rockyroadshub/ACFC/Essentials/Features/ACFC Device.gif

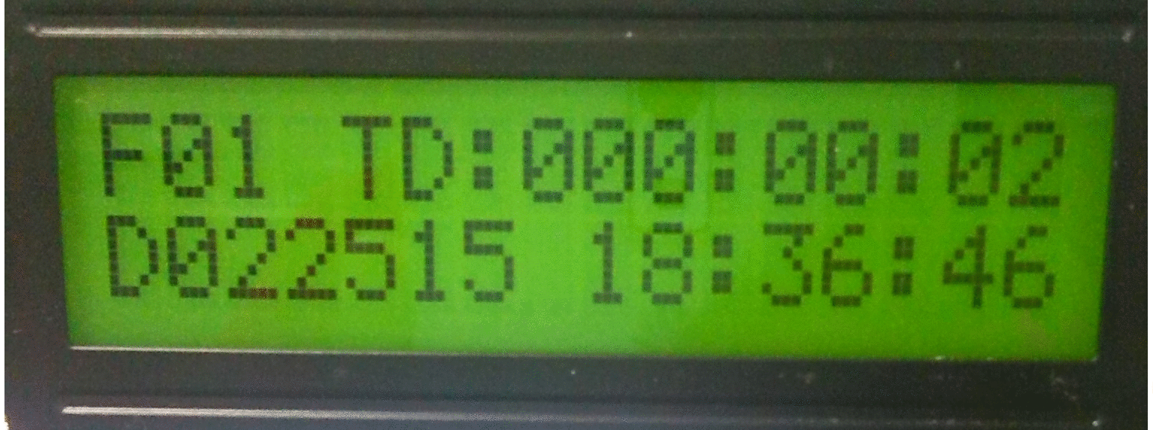
Essentials/Features/ACFC Device.gif
