rockyroadshub/ACFC/Essentials/Features/Device Lock.jpg

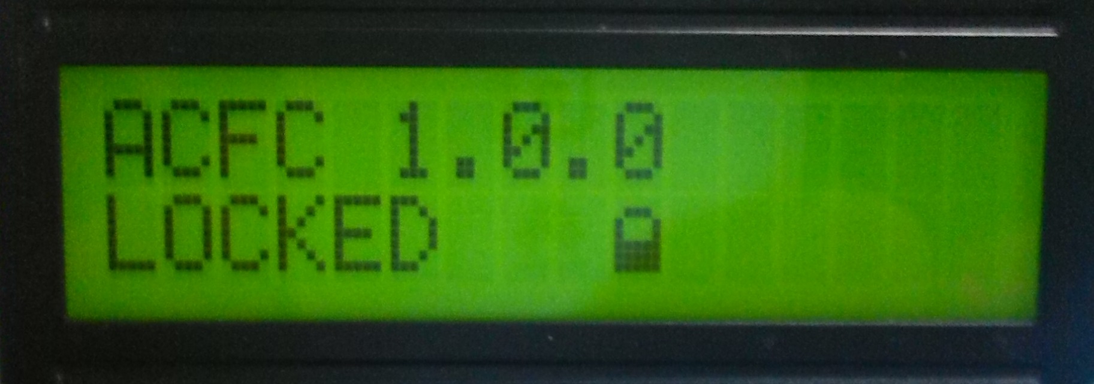
Essentials/Features/Device Lock.jpg
