rockyroadshub/ACFC/Essentials/Features/Device Unlock.jpg

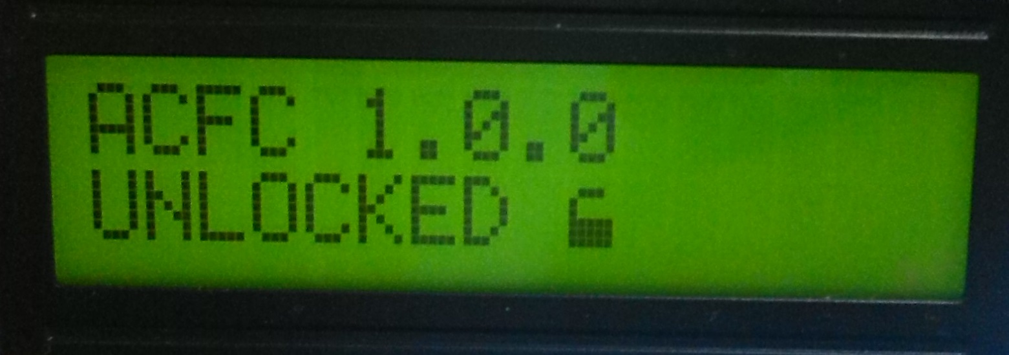
Essentials/Features/Device Unlock.jpg
