rockyroadshub/ACFC/Essentials/Features/Fluctuation Timer and Counter 1.jpg

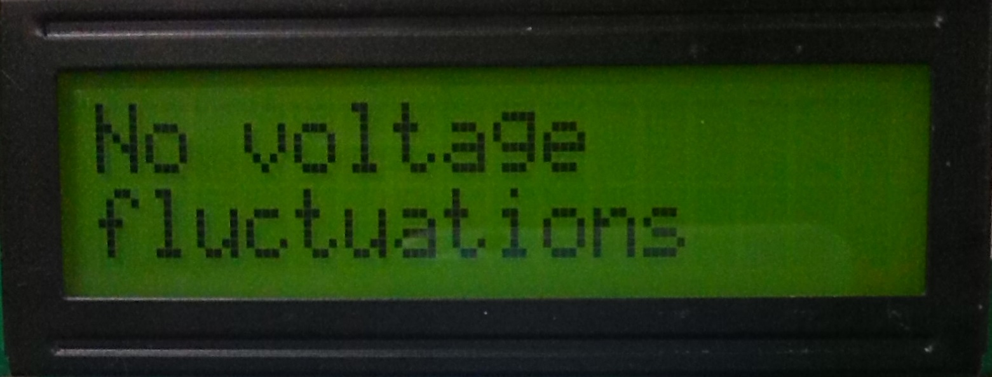
Essentials/Features/Fluctuation Timer and Counter 1.jpg
