rockyroadshub/ACFC/Essentials/Features/Fluctuation Timer and Counter 2.jpg

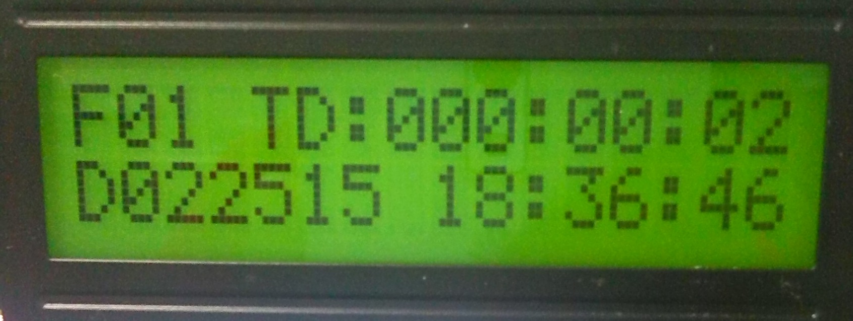
Essentials/Features/Fluctuation Timer and Counter 2.jpg
