rockyroadshub/ACFC/Essentials/Features/System Time and Date.jpg

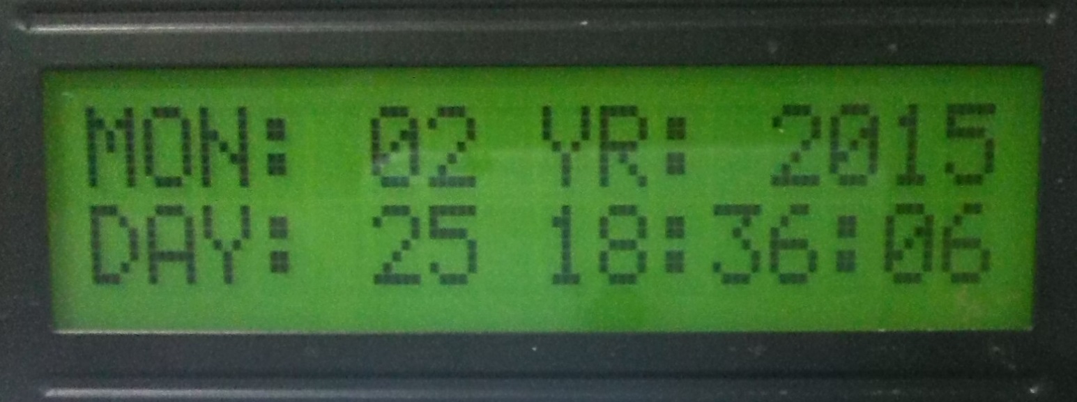
Essentials/Features/System Time and Date.jpg
