rockyroadshub/ACFC/Essentials/Model/ACFC.png

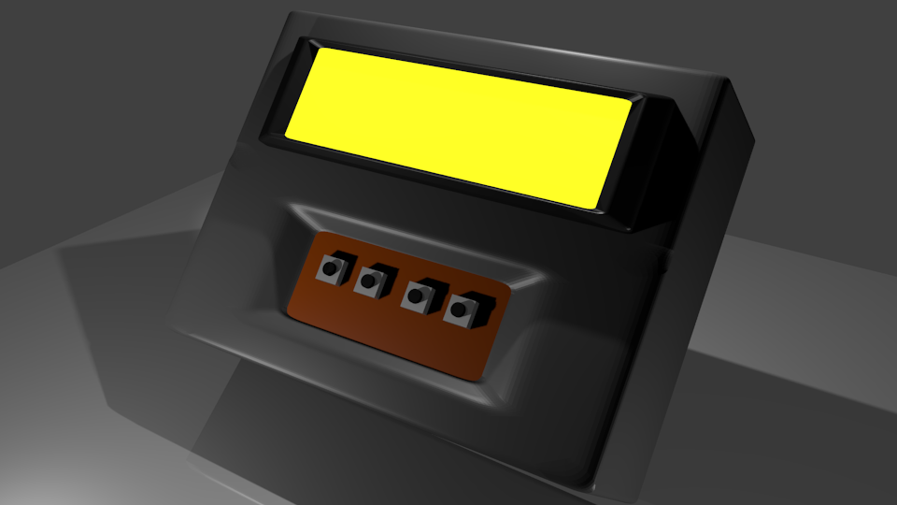
Essentials/Model/ACFC.png
