rockyroadshub/ACFC/Essentials/Others/Buttons.jpg

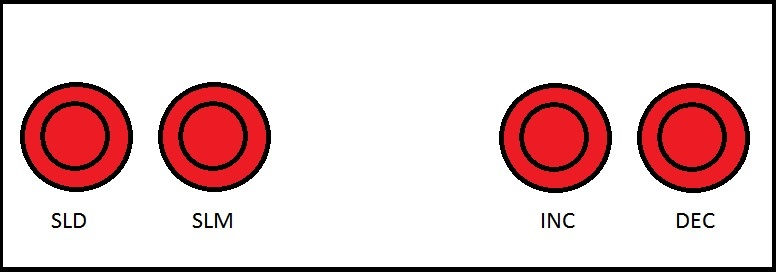
Essentials/Others/Buttons.jpg
