rockyroadshub/ACFC/Manuals/Gizduino Installation Guide.pdf

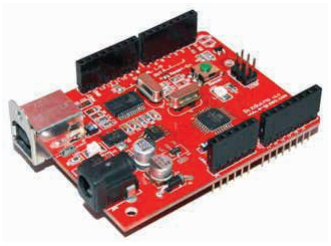
[picture p33: figure]
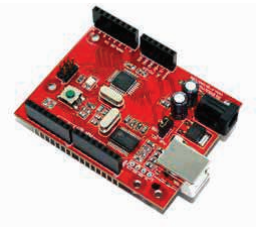
[picture p34: figure]

Page 1 of 4 Pages | gizDuino Installation Guide

# gizDuino

# Installation Guide

For gizDuino 168/328 Ver 3.0

gizDuino platform is based on open source Arduino platform designed by Massimo Banzi, et al. It is not an exact copy though, but the user will not notice any difference during normal use. Once the driver is successfully installed, the gizDuino will function exactly like an Arduino. The important thing is, the right driver must be installed in the right manner. Failure to do this simple procedure would almost certainly results in problems.

USB Interface

The Arduino uses an FT-232 chip as its USB bridge. In contrast, the gizDuino uses the PL-2303 chip. PL-2303 was picked over the FT-232 since they are easier to source, at least from our region. This difference will be visible to the user only during device driver installation.

!"#$%&'()'*+(&",,(#%-".*(-/0-(-/*(1+'-(-"2*(-/*(3"4-Duino is plugged in a PC, the Windows OS will automatically make an attempt to install its own driver. And will usually complete the procedure without 5033"#3(0#(*++%+6(7/*(8+%9,*2("':(3"4;)"#%(&",,(#%-( work with the Windows built-in driver. You must install the latest the driver provided with the gizDuino.

Figure 1. gizDuino 168/328 Ver. 3.0 now features automatic power source selection and an optiboot bootloader.

Figure 2. Previous versions of the gizDuino require the user to manually change jumper settings to switch to a different power source.

Copyright 2012 by e-Gizmo Mechatronix Central.

Arduino is an open source platform developed by the Arduino Team (Dave Mellis, Tom Igoe, Gianluca Martino, David Cuartielles, and Massimo Banzi) . www.arduino.cc

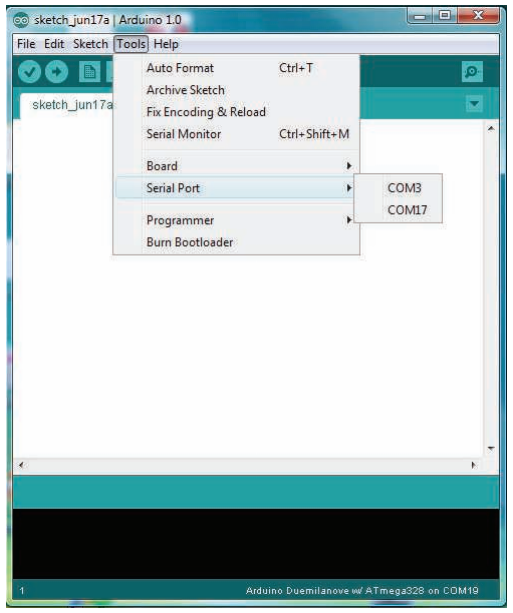
[picture p35: figure]
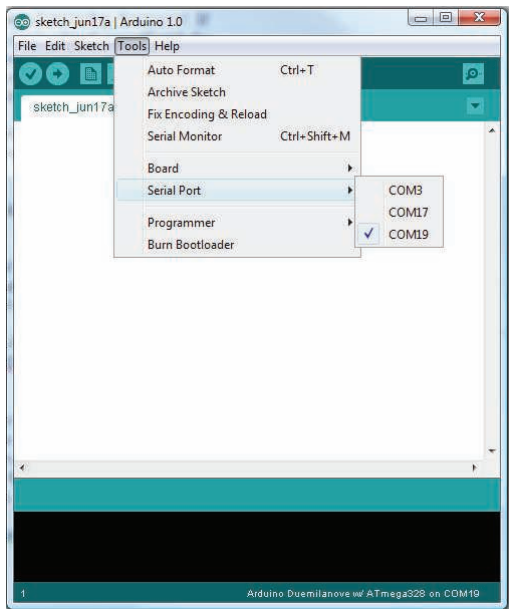
[picture p36: figure]

gizDuino Installation Guide | Page 2 of 4 Pages

Driver Installation

Driver installation must be done before connecting the gizDuino with your PC. But then,we have this "++*'"'-"9,*()+3*(%<(8,)33"#3(-/"#3'(1+'-(9*<%+*(+*0$-ing the manual. You already plugged your gizDuino, didn’t you? Not to worry, it is nothing to be embarrassed about. No permanent harm done either, it is just you burdened yourself with the extra work needed to undo your mistake – you have to uninstall the wrong driver. It is easy, just uninstall the PL-2303 com port appearing in your system device driver list. If you have no idea how to do this, have someone to do it for you.

7%("#'-0,,:(,%0$(-/*("#'-0,,0-"%#(=;(0#$(1#$(-/*(<%,$*+( with a PL2303 on its label, and run the setup.exe contained in it. Follow the setup instructions that 50'/*'(%#(>%)+('.+**#:(0#$(>%)(0+*($%#*6(

COM port Assignment

Don’t plug your gizDuino just yet, we have to determine what COM port it is assigned tyo:

1. Launch the Arduino IDE.

### 2. Click Tools>Serial Port and record the list of

available COM ports. (See Note 1)

### 3. Click anywhere within the Arduino IDE window

to close the drop menu.

### 4. Plug the gizDuino. Let the PC does its job of

recognizing the gizDuino. This may take a few seconds.

### 5. Click Tools>Serial Port once again and look

for a new COM port added to the list. This is the COM assignment of your gizDuino. Click to select if it is not marked with a check mark.

Figure 3. Available COM ports as displayed from my PC before the gizDuino is plugged in. See Note 1.

Figure 4. COM19 appears after plugging in my gizDuino. A different COM port may be assigned by your PC depending on its availability.

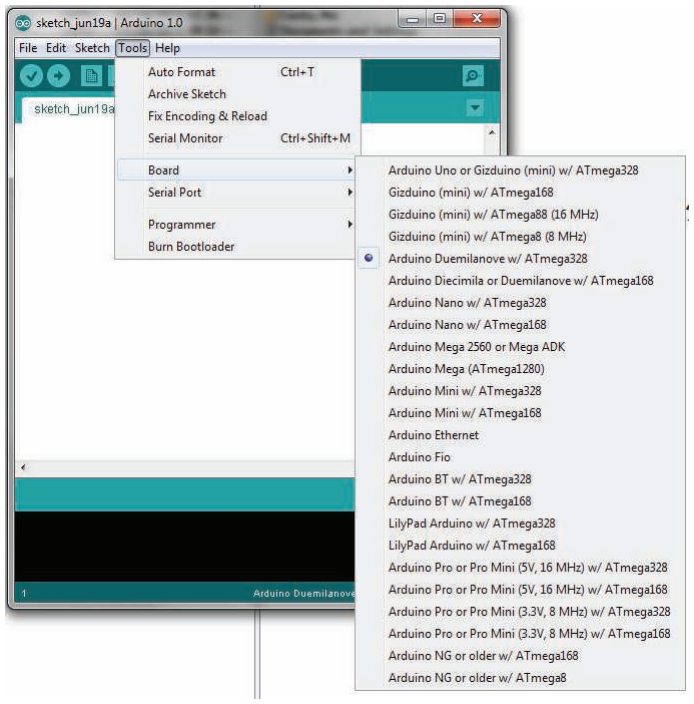
[picture p37: figure]

Page 3 of 4 Pages | gizDuino Installation Guide

Board Assigment

!*(0+*(0,2%'-(-/*+*6(7/*(1#0,('-*8(&",,(9*(-%(-*,,(-/*( Arduino IDE what Arduino hardware you are using. If you are using an Arduino IDE provided by e-Gizmo, just select the gizDuino model corresponding to your board. If you acquired it elsewhere, don’t look for gizDuino boards in the list, there is none. Select the equivalent as follows:

gizDuino 328 rev 3.0 -> Arduino Uno

If you are using and older version of gizDuino:

gizDuino 328
-> Arduino Duemilanove w/ ATmega328

gizDuino 168
-> Arduino Diecimila or Duemilanove w/ ATmega168

Your gizDuino is now ready to use! This procedure need to be done only once. Once the setup is correctly completed, your gizDuino will be remembered by the Arduino IDE for as long as you want it to be remembered.

Figure 5. Select the gizDuino model corresponding to your board. If the gizDuino boards do not appear in the list, select the Arduino equivalent as described in the text.

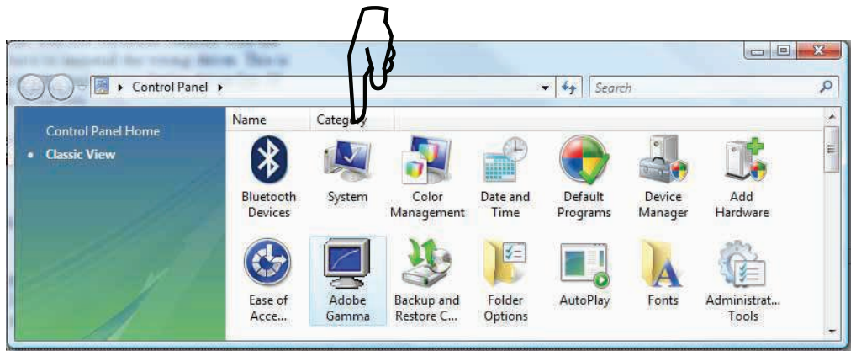
[picture p38: figure]
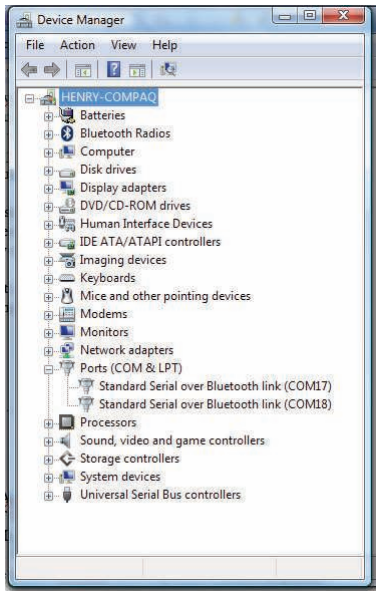
[picture p39: figure]

gizDuino Installation Guide | Page 4 of 4 Pages

Note 1:

The Arduino IDE can easily be distracted from too many unused COM port. If you use a lot of Bluetooth devices with your PC, chances are, your system is littered with too many COM port. This can slow down the port scanning of the Arduino IDE almost to a halt. You will notice this whenever you click Tools on the menu bar. It will take a long while before Arduino IDE responds with the drop menu.

To remedy this, uninstall all Bluetooth COM ports that are not in use.

Figure 6. If your Arduino IDE suddenly runs slow on click to the Tools menu, chances are your system is choked by too many COM ports assigned to unused Bluetooth devices. Check your system COM usage by clicking Control Panel>System>Device Drivers.

Figure 7. Click Ports to display COM ports usage. Remove all COM ports assigned to unused Bluetooth devices to speed up the Arduino.
