rockyroadshub/ACFC/Essentials/Others/Printer USB Connector.jpg

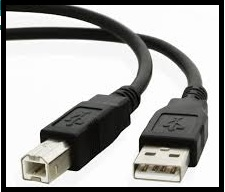
Essentials/Others/Printer USB Connector.jpg
