rockyroadshub/ACFC/Essentials/PCB/Button PCB/Etch/Button PCB_etch_silk_bottom.pdf

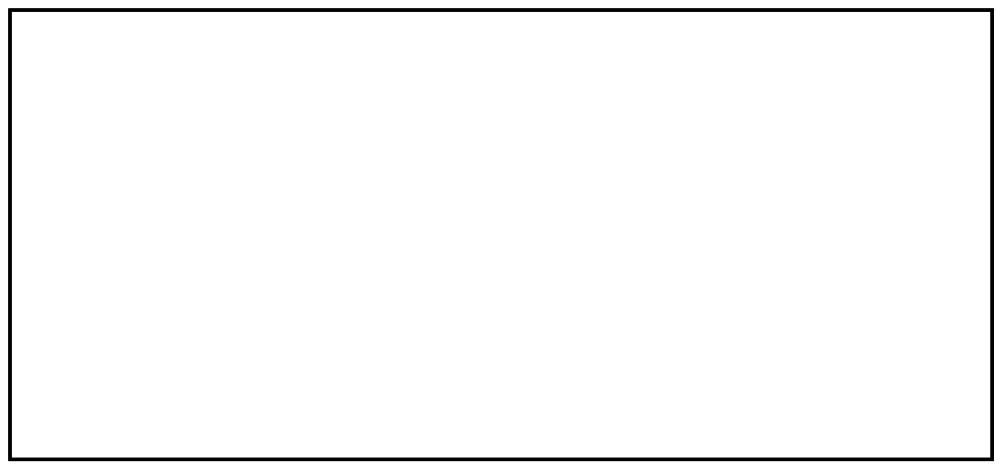
[picture p59: page 1]
