rockyroadshub/ACFC/Essentials/PCB/Button PCB/Etch/Button PCB_etch_silk_bottom_mirror.pdf

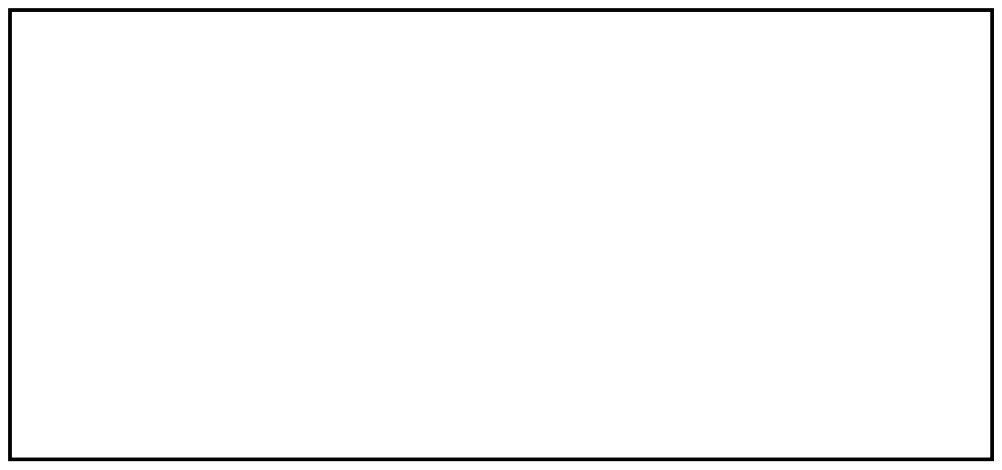
[picture p60: page 1]
