rockyroadshub/ACFC/Essentials/PCB/Button PCB/Etch/Button PCB_etch_silk_top.pdf

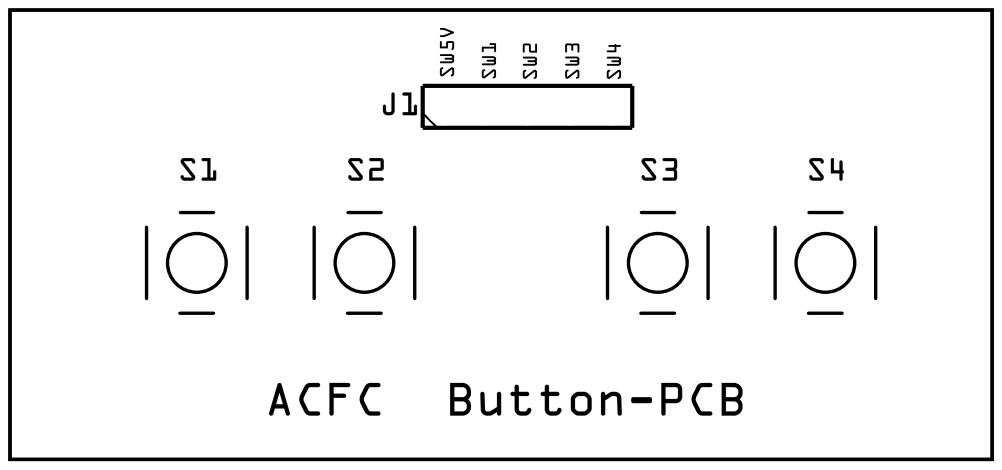
[picture p61: page 1]
