rockyroadshub/ACFC/Essentials/PCB/Button PCB/Etch/Button PCB_etch_silk_top_mirror.pdf

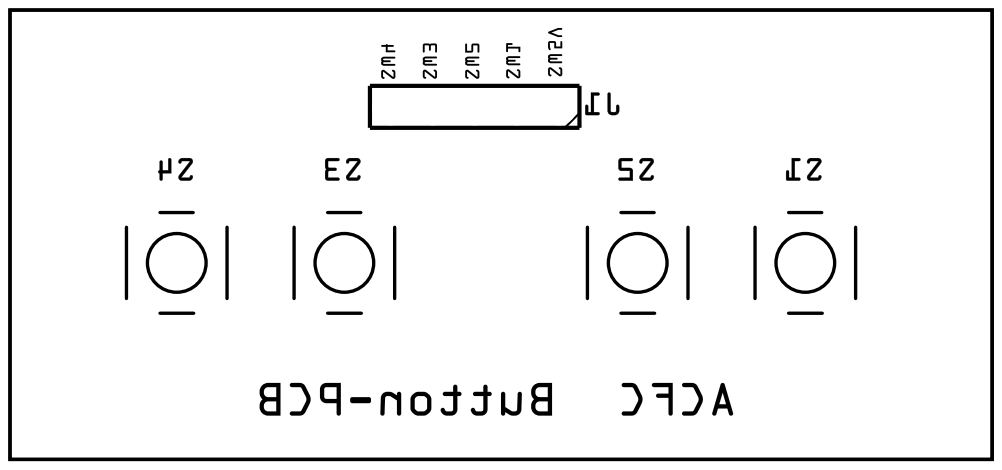
[picture p62: page 1]
