rockyroadshub/ACFC/Essentials/PCB/Main PCB/Etch/Main PCB_etch_copper_bottom_mirror.pdf

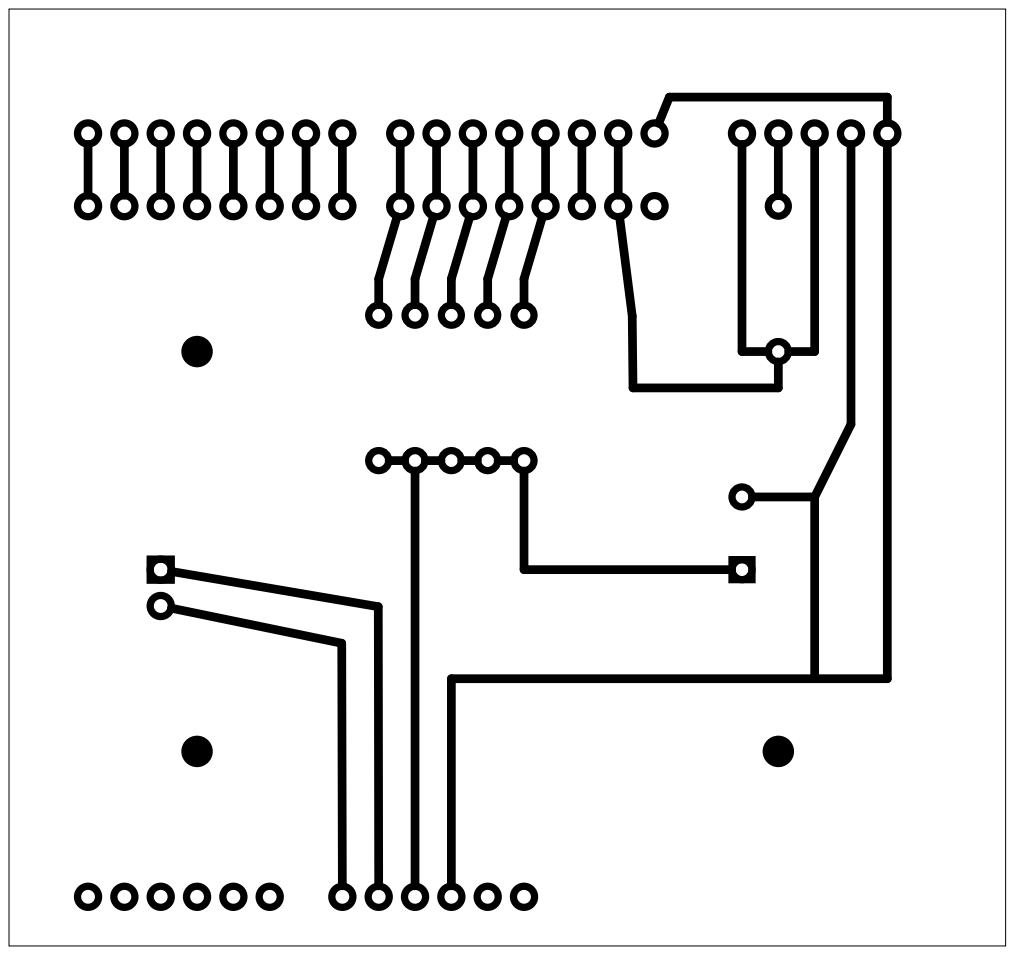
[picture p63: page 1]
