rockyroadshub/ACFC/Essentials/PCB/Main PCB/Etch/Main PCB_etch_copper_top.pdf

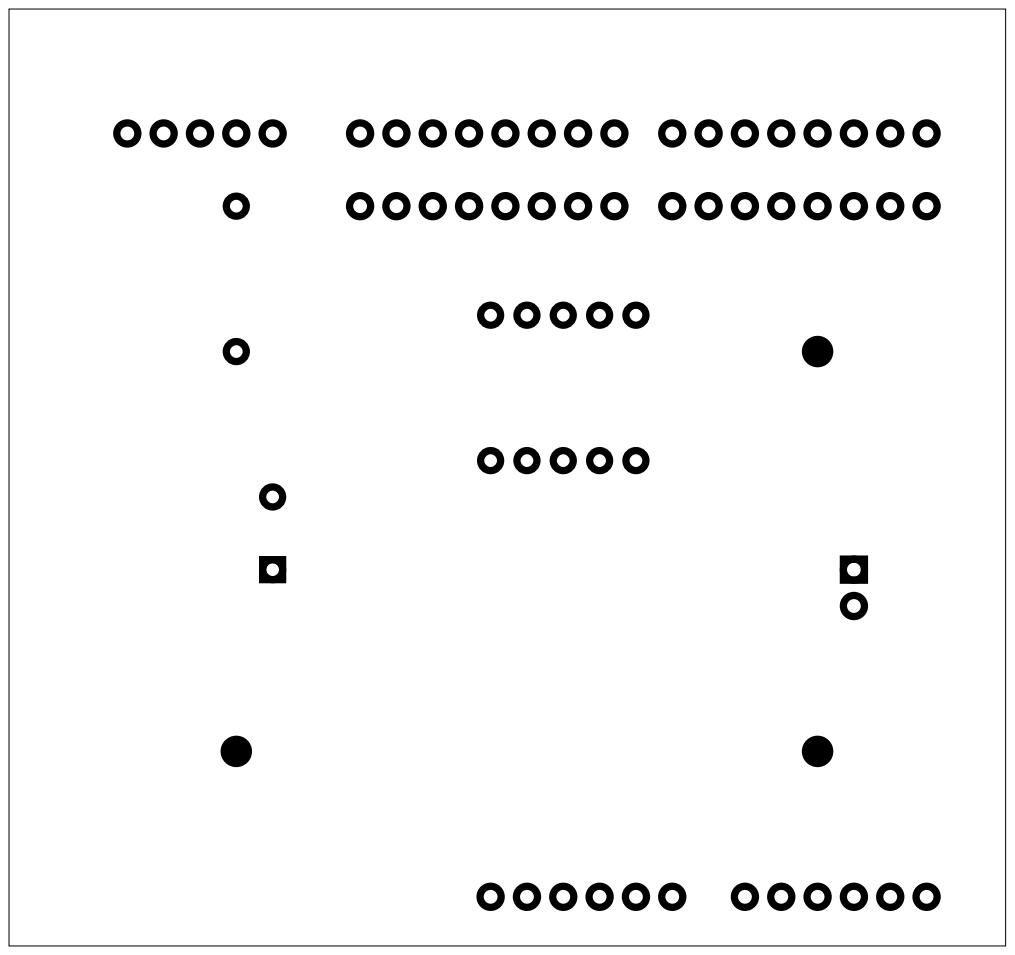
[picture p64: page 1]
