rockyroadshub/ACFC/Essentials/PCB/Main PCB/Etch/Main PCB_etch_copper_top_mirror.pdf

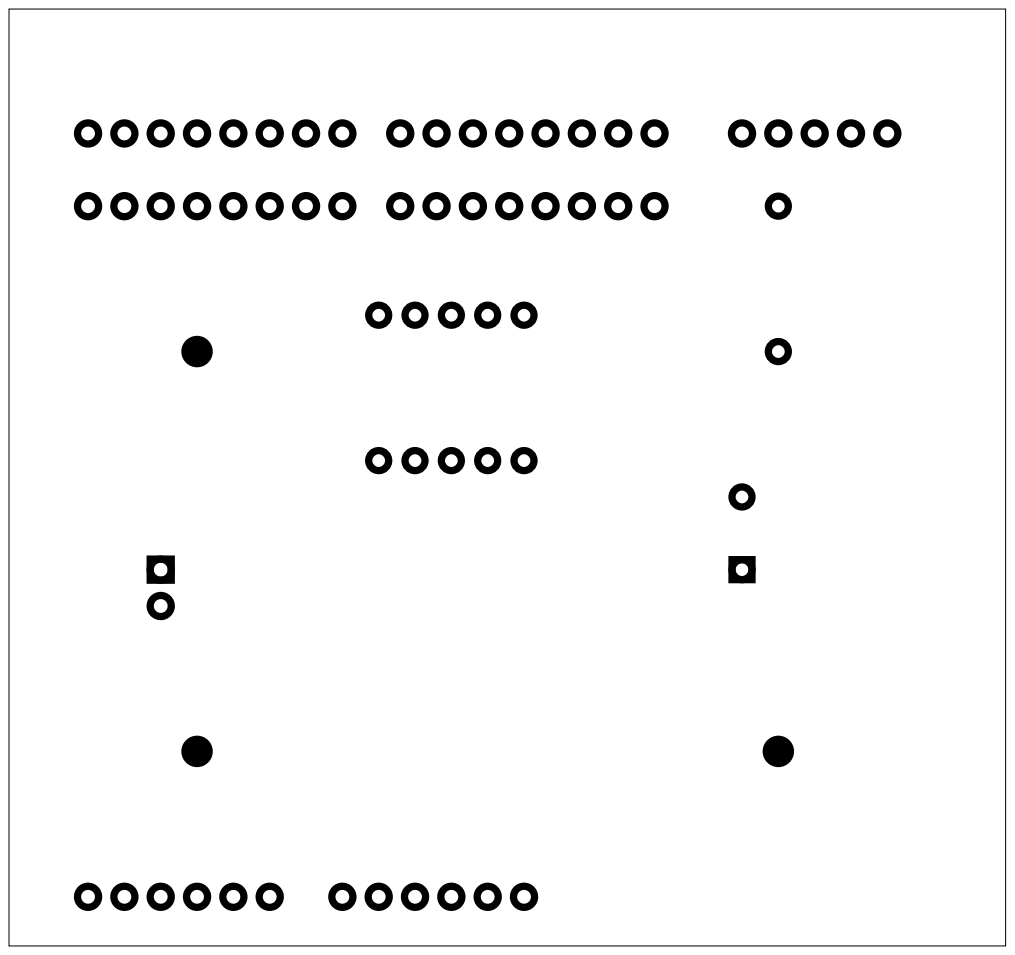
[picture p65: page 1]
