rockyroadshub/ACFC/Essentials/PCB/Main PCB/Etch/Main PCB_etch_mask_bottom.pdf

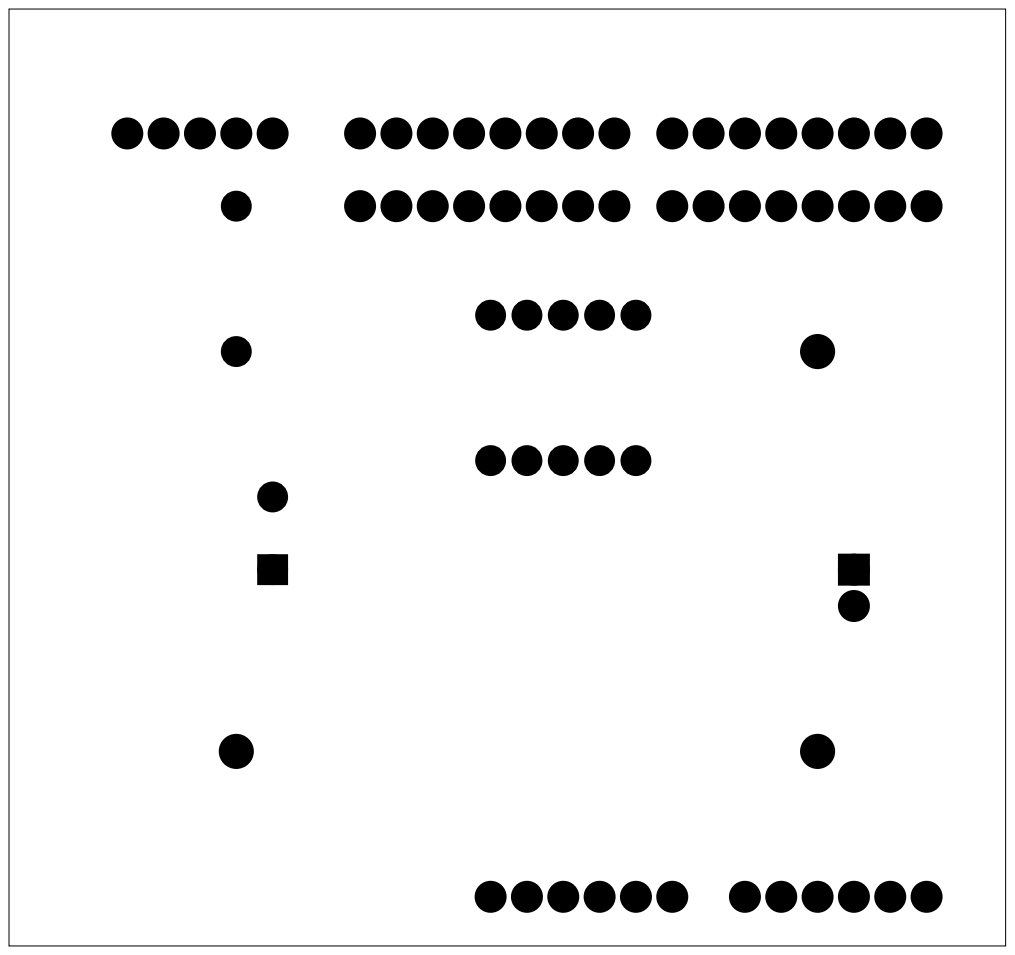
[picture p66: page 1]
