rockyroadshub/ACFC/Essentials/PCB/Main PCB/Etch/Main PCB_etch_mask_bottom_mirror.pdf

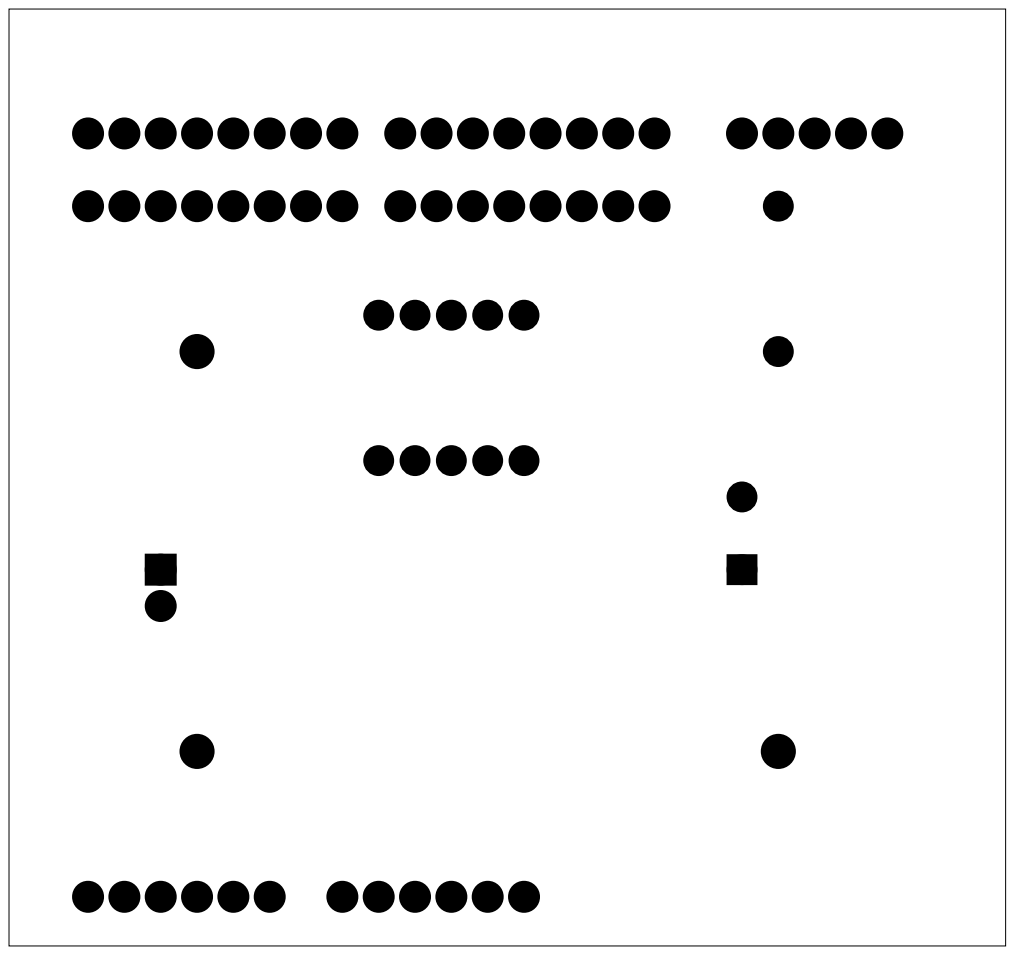
[picture p67: page 1]
