rockyroadshub/ACFC/Essentials/PCB/Main PCB/Etch/Main PCB_etch_silk_bottom.pdf

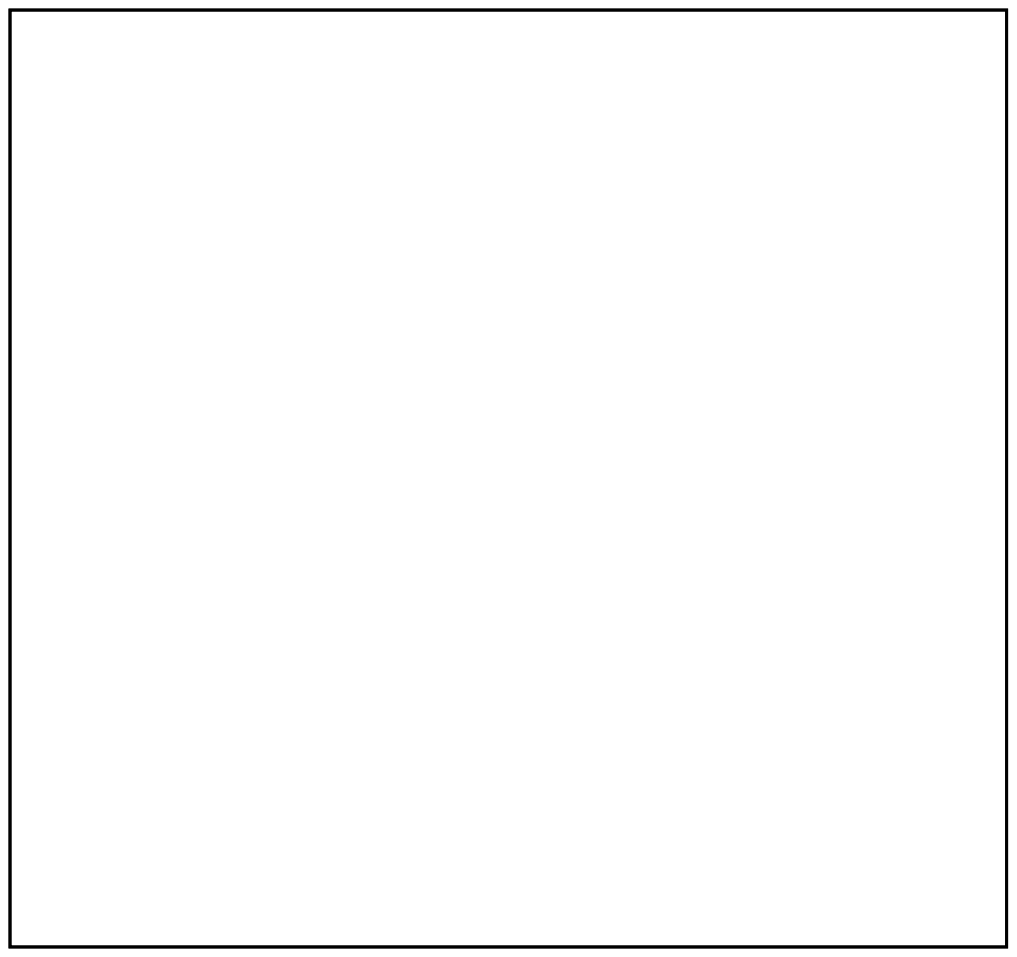
[picture p68: page 1]
