rockyroadshub/ACFC/Essentials/PCB/Main PCB/Etch/Main PCB_etch_silk_top.pdf

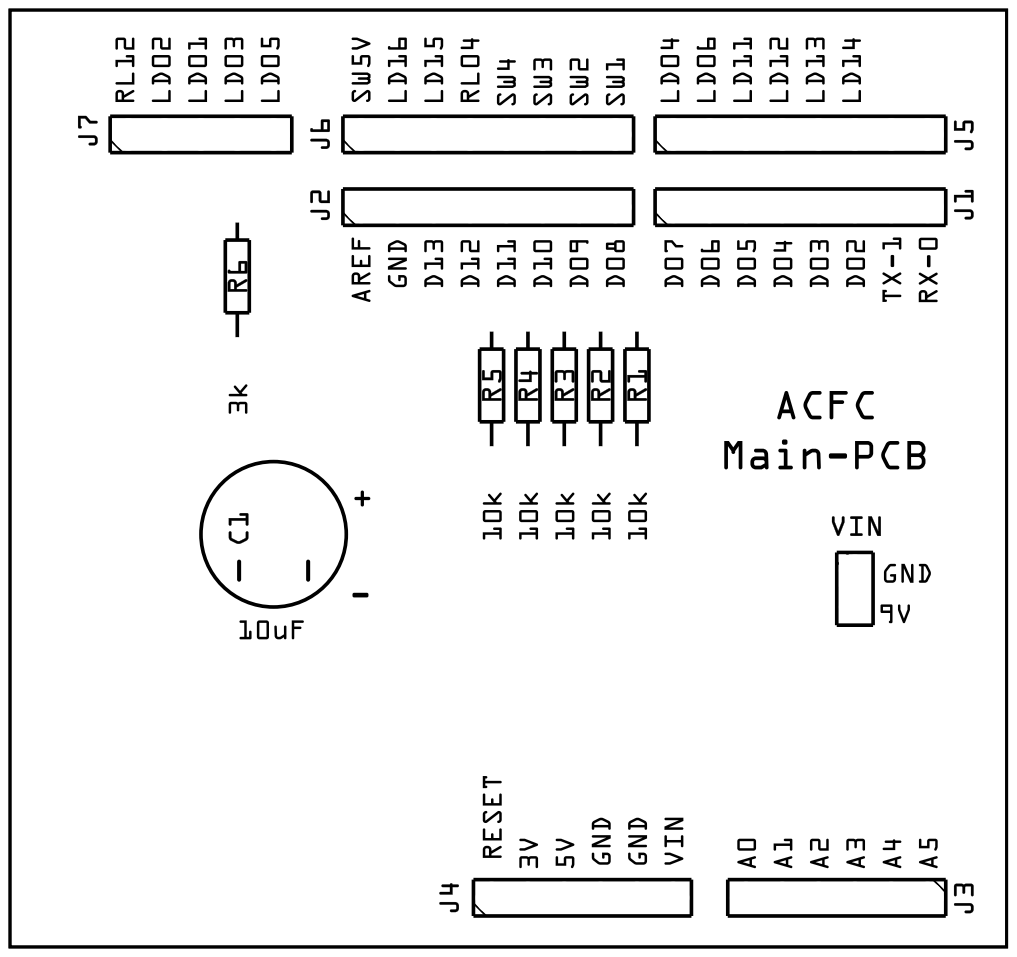
[picture p69: page 1]
