rockyroadshub/ACFC/Essentials/PCB/Main PCB/Etch/Main PCB_etch_silk_top_mirror.pdf

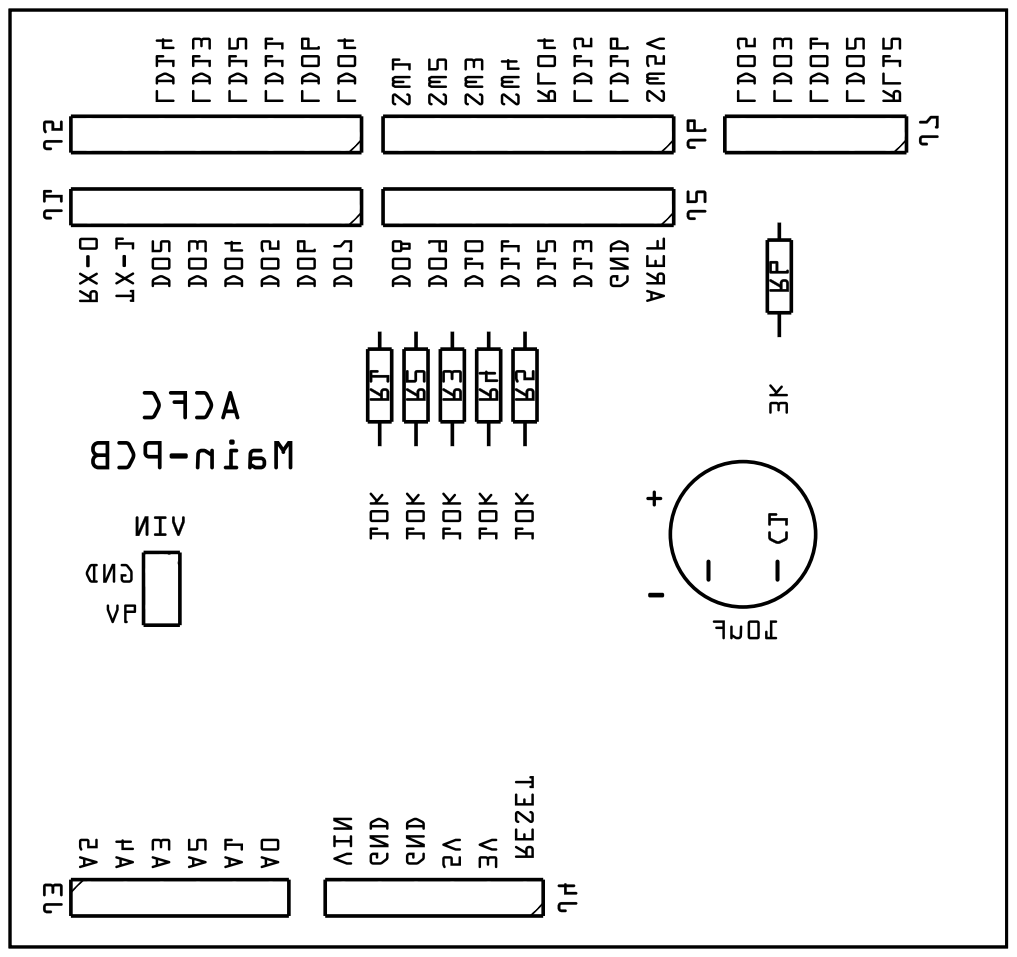
[picture p70: page 1]
